RealCorebb/bbTalkie/assets/byebye.gif

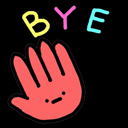
assets/byebye.gif
