RealCorebb/bbTalkie/esp-idf/src/main/include/sound.h

const unsigned char boot[] = {
0x00, 0x00, 0x00, 0x00, 0xFF, 0xFF, 0x01, 0x00, 0xFF, 0xFF, 0x01, 0x00, 
0x00, 0x00, 0x00, 0x00, 0xFF, 0xFF, 0x01, 0x00, 0xFE, 0xFF, 0x04, 0x00, 
0xFC, 0xFF, 0x03, 0x00, 0xFE, 0xFF, 0x01, 0x00, 0xFF, 0xFF, 0x01, 0x00, 
0x00, 0x00, 0xFF, 0xFF, 0x02, 0x00, 0xFC, 0xFF, 0x04, 0x00, 0xFD, 0xFF, 
0x03, 0x00, 0xFE, 0xFF, 0x00, 0x00, 0x01, 0x00, 0xFE, 0xFF, 0x03, 0x00, 
0xFD, 0xFF, 0x03, 0x00, 0xFD, 0xFF, 0x03, 0x00, 0xFD, 0xFF, 0x03, 0x00, 
0xFC, 0xFF, 0x05, 0x00, 0xFC, 0xFF, 0x03, 0x00, 0xFD, 0xFF, 0x02, 0x00, 
0x00, 0x00, 0xFE, 0xFF, 0x04, 0x00, 0xFB, 0xFF, 0x05, 0x00, 0xFD, 0xFF, 
0x01, 0x00, 0x00, 0x00, 0x00, 0x00, 0x00, 0x00, 0x00, 0x00, 0x00, 0x00, 
0x00, 0x00, 0x00, 0x00, 0x00, 0x00, 0x00, 0x00, 0xFF, 0xFF, 0x02, 0x00, 
0xFE, 0xFF, 0x02, 0x00, 0xFF, 0xFF, 0xFF, 0xFF, 0x02, 0x00, 0xFE, 0xFF, 
0x03, 0x00, 0xFC, 0xFF, 0x04, 0x00, 0xFD, 0xFF, 0x02, 0x00, 0xFE, 0xFF, 
0x02, 0x00, 0xFE, 0xFF, 0x02, 0x00, 0xFF, 0xFF, 0xFE, 0xFF, 0x05, 0x00, 
0xF9, 0xFF, 0x08, 0x00, 0xF9, 0xFF, 0x05, 0x00, 0xFD, 0xFF, 0x02, 0x00, 
0xFF, 0xFF, 0x01, 0x00, 0xFF, 0xFF, 0x00, 0x00, 0x01, 0x00, 0x00, 0x00, 
0xFF, 0xFF, 0x00, 0x00, 0xFF, 0xFF, 0x03, 0x00, 0xFD, 0xFF, 0x02, 0x00, 
0xFE, 0xFF, 0x01, 0x00, 0x00, 0x00, 0x00, 0x00, 0x00, 0x00, 0x00, 0x00, 
0x00, 0x00, 0xFF, 0xFF, 0x01, 0x00, 0x01, 0x00, 0xFD, 0xFF, 0x04, 0x00, 
0xFB, 0xFF, 0x05, 0x00, 0xFD, 0xFF, 0x00, 0x00, 0x02, 0x00, 0xFD, 0xFF, 
0x04, 0x00, 0xFC, 0xFF, 0x03, 0x00, 0xFD, 0xFF, 0x03, 0x00, 0xFE, 0xFF, 
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
0x4F, 0x02, 0x39, 0x02, 0xEE, 0x01, 0xE4, 0x00, 0x4F, 0x01, 0xE0, 0x01, 
0xA6, 0x01, 0xC6, 0x00, 0xA3, 0xFF, 0x67, 0xFF, 0xC5, 0xFE, 0x41, 0x00, 
0xF7, 0xFF, 0xE2, 0x00, 0x79, 0x00, 0x83, 0x01, 0x09, 0x01, 0xCE, 0xFF, 
0x67, 0x00, 0x28, 0x00, 0x0A, 0x02, 0xF9, 0x01, 0x5F, 0x03, 0x80, 0x02, 
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
};
